beni045/gesture_controlled_robot_pet/RaspberryPi_robot_pet/deactivate.jpg

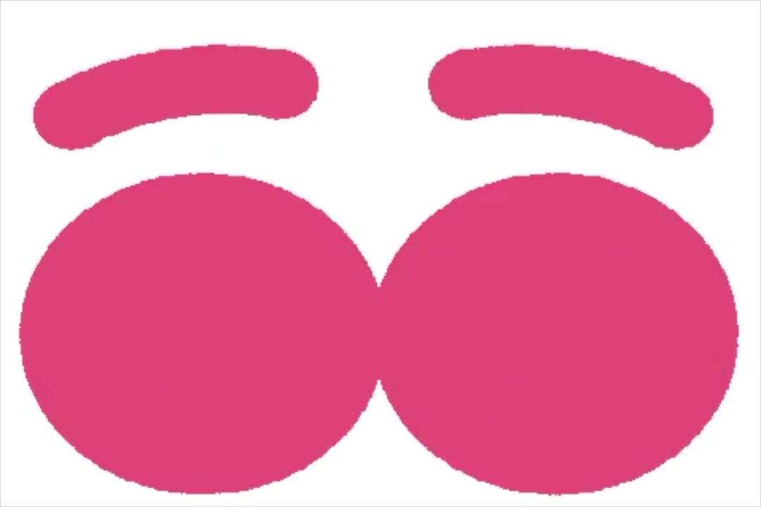
RaspberryPi_robot_pet/deactivate.jpg
