beni045/gesture_controlled_robot_pet/RaspberryPi_robot_pet/follow_img.jpg

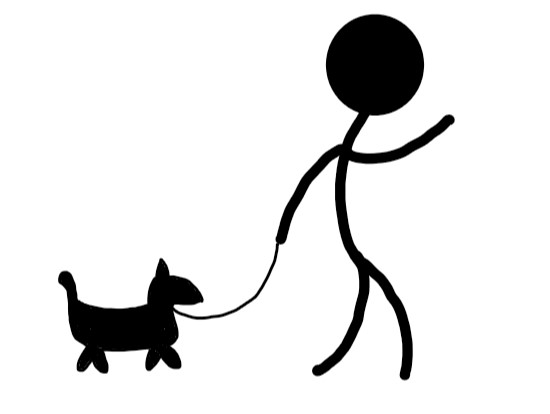
RaspberryPi_robot_pet/follow_img.jpg
